joelsernamoreno/EvilCrow-RF/3D_Case_Satan/img/V1_CASE_New_Style_1.jpg

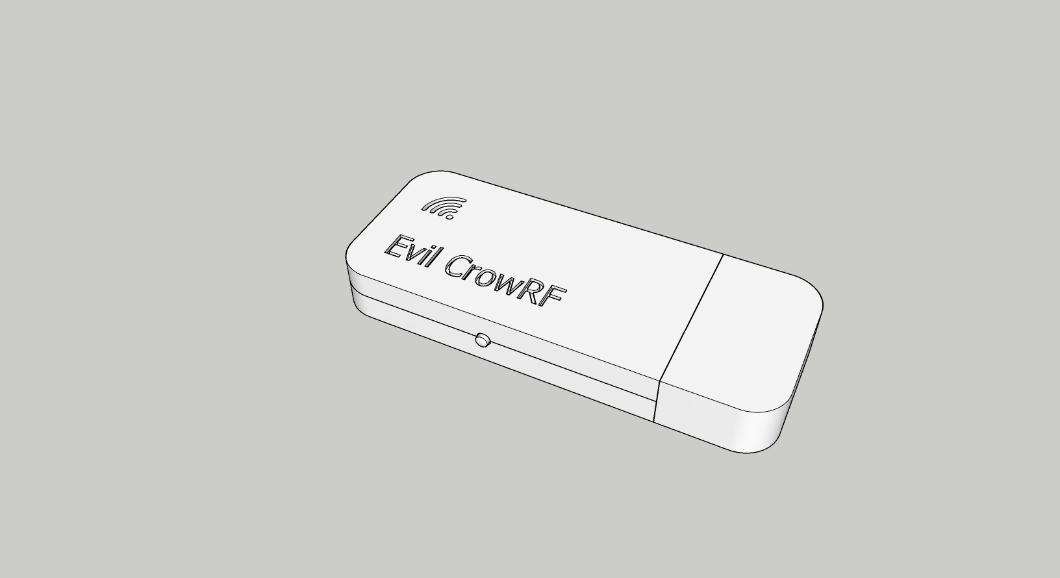
3D_Case_Satan/img/V1_CASE_New_Style_1.jpg
